yasitha18243/e16-3yp-water-quality-monitoring-and-usage-monitoring-system/designs/circuit designs/Module 1/1.PNG

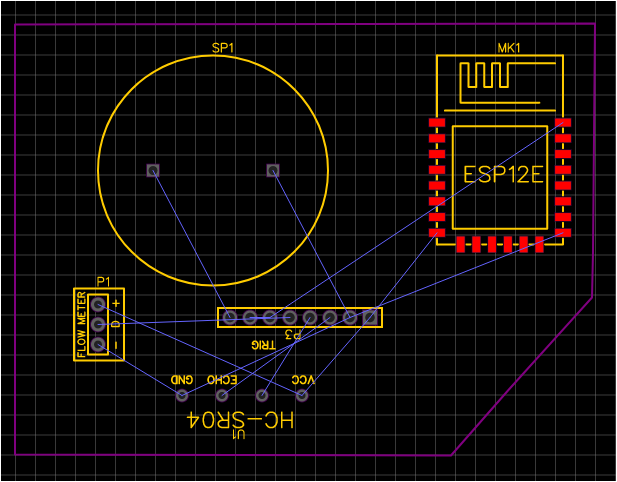
designs/circuit designs/Module 1/1.PNG
