yasitha18243/e16-3yp-water-quality-monitoring-and-usage-monitoring-system/designs/circuit designs/Module 2/2.PNG

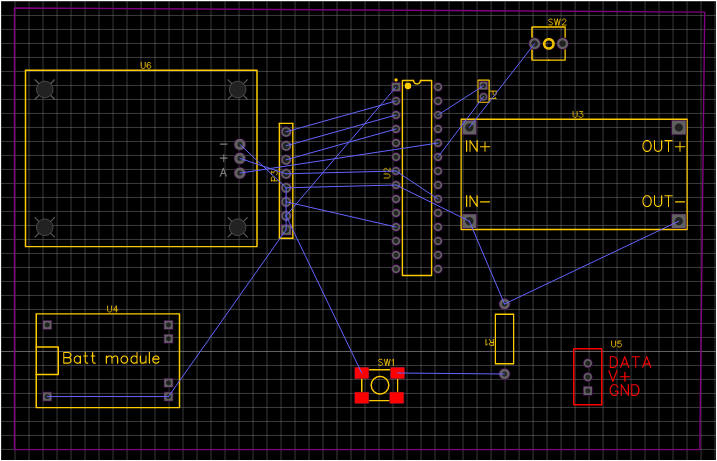
designs/circuit designs/Module 2/2.PNG
