yasitha18243/e16-3yp-water-quality-monitoring-and-usage-monitoring-system/designs/water quality monitoring/3.PNG

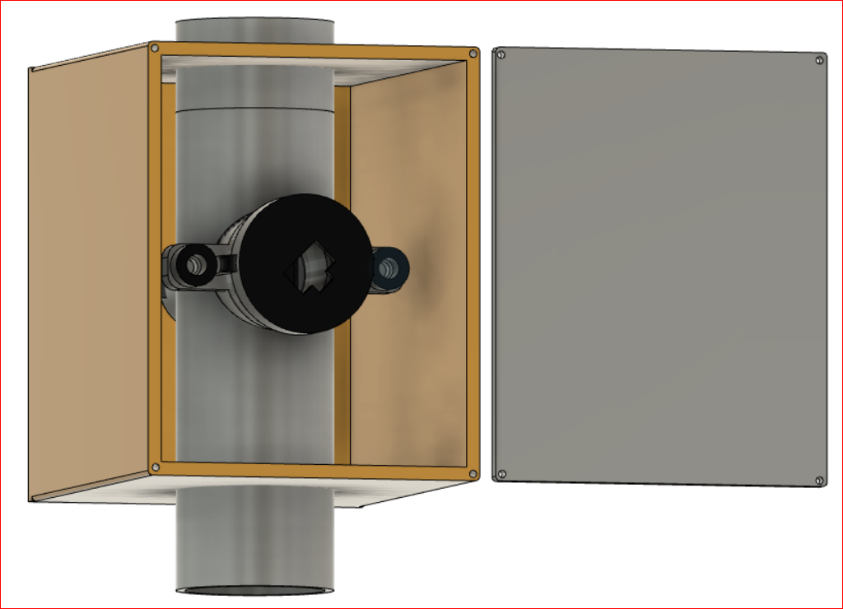
designs/water quality monitoring/3.PNG
